graysonguarino/rustino-stepseq/schematic/schematic.kicad_sch

## KiCad design schematic/schematic.kicad_sch (2025-10-31)

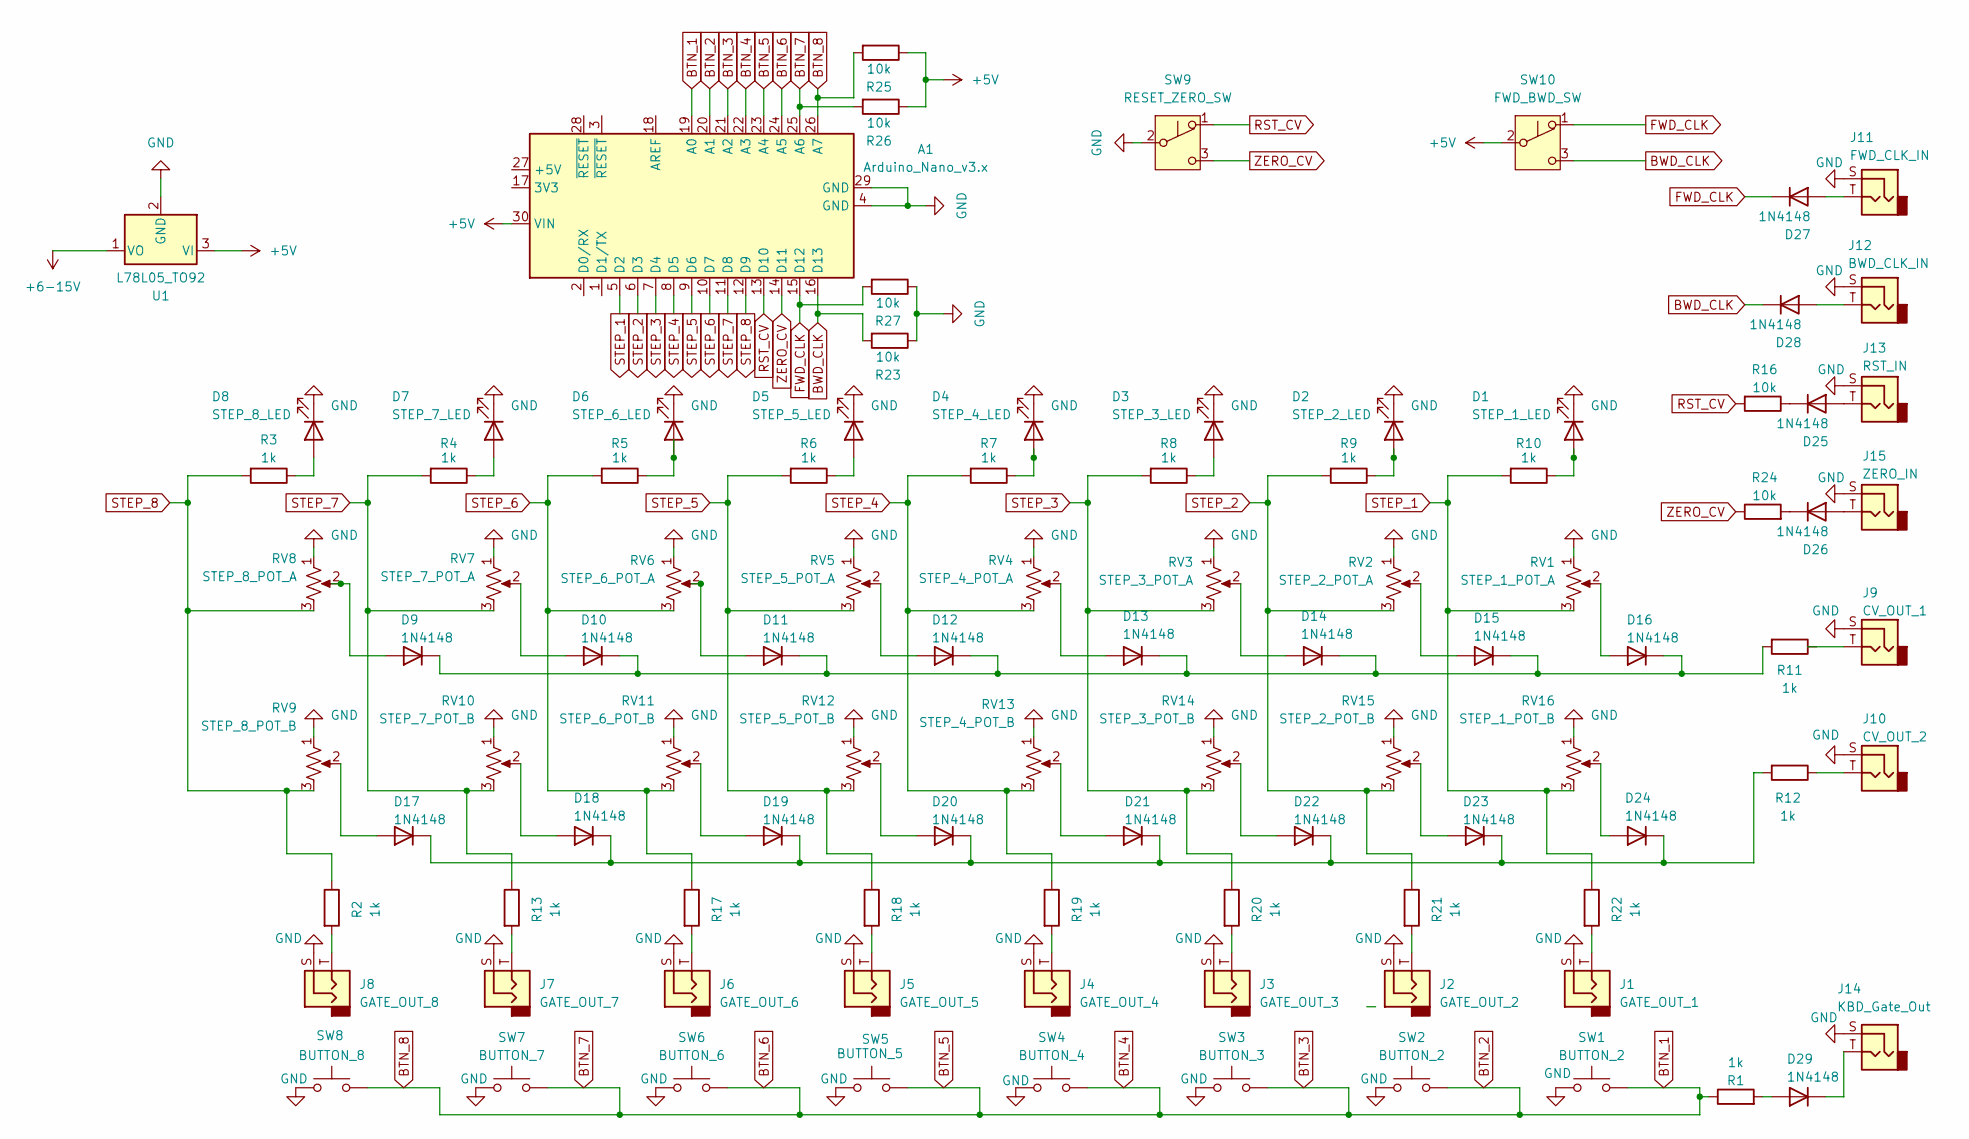
[picture p6: schematic schematic.kicad_sch]

Parts:
A1: Arduino_Nano_v3.x; Arduino_Nano
D1: STEP_1_LED
D2: STEP_2_LED
D3: STEP_3_LED
D4: STEP_4_LED
D5: STEP_5_LED
D6: STEP_6_LED
D7: STEP_7_LED
D8: STEP_8_LED
D9, D10, D11, D12, D13, D14, D15, D16, D17, D18, D19, D20, D21, D22, D23, D24, D25, D26, D27, D28, D29: 1N4148; D_DO-35_SOD27_P7.62mm_Horizontal
J1: GATE_OUT_1
J2: GATE_OUT_2
J3: GATE_OUT_3
J4: GATE_OUT_4
J5: GATE_OUT_5
J6: GATE_OUT_6
J7: GATE_OUT_7
J8: GATE_OUT_8
J9: CV_OUT_1
J10: CV_OUT_2
J11: FWD_CLK_IN
J12: BWD_CLK_IN
J13: RST_IN
J14: KBD_Gate_Out
J15: ZERO_IN
R1, R2, R3, R4, R5, R6, R7, R8, R9, R10, R11, R12, R13, R17, R18, R19, R20, R21, R22: 1k
R16, R23, R24, R25, R26, R27: 10k
RV1: STEP_1_POT_A
RV2: STEP_2_POT_A
RV3: STEP_3_POT_A
RV4: STEP_4_POT_A
RV5: STEP_5_POT_A
RV6: STEP_6_POT_A
RV7: STEP_7_POT_A
RV8: STEP_8_POT_A
RV9: STEP_8_POT_B
RV10: STEP_7_POT_B
RV11: STEP_6_POT_B
RV12: STEP_5_POT_B
RV13: STEP_4_POT_B
RV14: STEP_3_POT_B
RV15: STEP_2_POT_B
RV16: STEP_1_POT_B
SW1, SW2: BUTTON_2
SW3: BUTTON_3
SW4: BUTTON_4
SW5: BUTTON_5
SW6: BUTTON_6
SW7: BUTTON_7
SW8: BUTTON_8
SW9: RESET_ZERO_SW
SW10: FWD_BWD_SW
U1: L78L05_TO92; TO-92_Inline

Connections:
+5V: A1.30 (VIN), R25.1, R26.1, SW10.2 (B), U1.3 (VI)
+6-15V: U1.1 (VO)
BTN_1: A1.19 (A0), A1.20 (A1), A1.21 (A2), A1.22 (A3), A1.23 (A4), A1.24 (A5), A1.25 (A6), A1.26 (A7), R1.1, R25.2, R26.2, SW1.2, SW2.2, SW3.2, SW4.2, SW5.2, SW6.2, SW7.2, SW8.2
BWD_CLK: A1.16 (D13), D28.1 (K), R23.2, SW10.3 (C)
FWD_CLK: A1.15 (D12), D27.1 (K), R27.2, SW10.1 (A)
GND: A1.4 (GND), A1.29 (GND), D1.1 (K), D2.1 (K), D3.1 (K), D4.1 (K), D5.1 (K), D6.1 (K), D7.1 (K), D8.1 (K), J1.S, J2.S, J3.S, J4.S, J5.S, J6.S, J7.S, J8.S, J9.S, J10.S, J11.S, J12.S, J13.S, J14.S, J15.S, R23.1, R27.1, RV1.1, RV2.1, RV3.1, RV4.1, RV5.1, RV6.1, RV7.1, RV8.1, RV9.1, RV10.1, RV11.1, RV12.1, RV13.1, RV14.1, RV15.1, RV16.1, SW1.1, SW2.1, SW3.1, SW4.1, SW5.1, SW6.1, SW7.1, SW8.1, SW9.2 (B), U1.2 (GND)
unnamed: D1.2 (A), R10.1
unnamed: D2.2 (A), R9.1
unnamed: D3.2 (A), R8.1
unnamed: D4.2 (A), R7.1
unnamed: D5.2 (A), R6.1
unnamed: D6.2 (A), R5.1
unnamed: D7.2 (A), R4.1
unnamed: D8.2 (A), R3.1
unnamed: D9.2 (A), RV8.2
unnamed: D9.1 (K), D10.1 (K), D11.1 (K), D12.1 (K), D13.1 (K), D14.1 (K), D15.1 (K), D16.1 (K), R11.2
unnamed: D10.2 (A), RV7.2
unnamed: D11.2 (A), RV6.2
unnamed: D12.2 (A), RV5.2
unnamed: D13.2 (A), RV4.2
unnamed: D14.2 (A), RV3.2
unnamed: D15.2 (A), RV2.2
unnamed: D16.2 (A), RV1.2
unnamed: D17.1 (K), D18.1 (K), D19.1 (K), D20.1 (K), D21.1 (K), D22.1 (K), D23.1 (K), D24.1 (K), R12.2
unnamed: D17.2 (A), RV9.2
unnamed: D18.2 (A), RV10.2
unnamed: D19.2 (A), RV11.2
unnamed: D20.2 (A), RV12.2
unnamed: D21.2 (A), RV13.2
unnamed: D22.2 (A), RV14.2
unnamed: D23.2 (A), RV15.2
unnamed: D24.2 (A), RV16.2
unnamed: D25.1 (K), R16.1
unnamed: D25.2 (A), J13.T
unnamed: D26.1 (K), R24.2
unnamed: D26.2 (A), J15.T
unnamed: D27.2 (A), J11.T
unnamed: D28.2 (A), J12.T
unnamed: D29.1 (K), J14.T
unnamed: D29.2 (A), R1.2
unnamed: J1.T, R22.2
unnamed: J2.T, R21.2
unnamed: J3.T, R20.2
unnamed: J4.T, R19.2
unnamed: J5.T, R18.2
unnamed: J6.T, R17.2
unnamed: J7.T, R13.2
unnamed: J8.T, R2.2
unnamed: J10.T, R12.1
RST_CV: A1.13 (D10), R16.2, SW9.1 (A)
STEP_1: A1.5 (D2), R10.2, R22.1, RV1.3, RV16.3
STEP_2: A1.6 (D3), R9.2, R21.1, RV2.3, RV15.3
STEP_3: A1.7 (D4), R8.2, R20.1, RV3.3, RV14.3
STEP_4: A1.8 (D5), R7.2, R19.1, RV4.3, RV13.3
STEP_5: A1.9 (D6), R6.2, R18.1, RV5.3, RV12.3
STEP_6: A1.10 (D7), R5.2, R17.1, RV6.3, RV11.3
STEP_7: A1.11 (D8), R4.2, R13.1, RV7.3, RV10.3
STEP_8: A1.12 (D9), R2.1, R3.2, RV8.3, RV9.3
ZERO_CV: A1.14 (D11), R24.1, SW9.3 (C)
